CuriousTech/WiFiWaterbedHeater3/Waterbed3/THSensor.cpp

#include "THSensor.h"
#include "Display.h"
#include "eeMem.h"
#include <Wire.h>

extern void WsSend(String s);
extern void sendState(void);

THSensor::THSensor()
{ 
}

void THSensor::init()
{
  Wire.begin(11, 10, 100000); // 10,11 also used by RTC and IMU
}

void THSensor::service()
{
  static uint8_t read_delay = 2;
  static uint8_t errCnt = 0;

  if(--read_delay)
    return;

  int16_t temp;
  int16_t rh;
  if(am.measure(temp, rh))
  {
    if(!ee.bCF)
      temp = temp * 9 / 5 + 320;
    tempMedian.add(temp);
    if (tempMedian.getMedian(temp) == tempMedian.OK)
    {
      m_temp = temp;
      m_rh = rh;
    }
    errCnt = 0;
  }
  else
  {
    if(errCnt < 5)
      errCnt++;
    else
    {
      IPAddress ip;
      display.Notify("AM2320 Error", ip); // be annoying
    }
  }

  read_delay = 5; // update every 5 seconds
}
