CuriousTech/WiFiWaterbedHeater3/Waterbed3/digitalFont.h

//
//

const uint8_t DIGIRT_18pt7bBitmaps[] PROGMEM = {
  0x00, 0x04, 0x30, 0xC3, 0x0C, 0x31, 0xC7, 0x1C, 0x61, 0x84, 0x30, 0xE3,
  0x0C, 0x30, 0xC7, 0x18, 0x60, 0x04, 0x38, 0x40, 0x69, 0xFF, 0xBE, 0x50,
  0x03, 0xFF, 0x01, 0xFF, 0xE0, 0xFF, 0xFC, 0x79, 0xCF, 0x1E, 0x77, 0x87,
  0xDD, 0xE1, 0xF6, 0xF8, 0x7F, 0xFE, 0x1B, 0xFB, 0x8E, 0x7C, 0xE3, 0x9E,
  0x30, 0xFF, 0xFC, 0x1F, 0xFE, 0x0F, 0xFF, 0x83, 0x1C, 0x71, 0xCF, 0x98,
  0x77, 0xEE, 0x1F, 0xFF, 0x87, 0xFB, 0xE1, 0xEE, 0xF8, 0xFB, 0xBE, 0x3C,
  0xE7, 0x0E, 0x39, 0xC1, 0xFF, 0xE0, 0x3F, 0xF0, 0x00, 0x00, 0x20, 0x00,
  0x70, 0x00, 0xF0, 0x07, 0xFE, 0x0F, 0xFF, 0x1F, 0xFC, 0x30, 0xE0, 0x30,
  0xE0, 0x31, 0xC0, 0x39, 0xC0, 0x31, 0xC0, 0x70, 0x80, 0x70, 0x80, 0x70,
  0x80, 0x7F, 0xF8, 0x3F, 0xFC, 0x1F, 0xFC, 0x03, 0x0C, 0x03, 0x1C, 0x03,
  0x1C, 0x07, 0x1C, 0x07, 0x1C, 0x07, 0x1C, 0x07, 0x18, 0x07, 0x18, 0x7F,
  0xF8, 0xFF, 0xF0, 0x7F, 0xE0, 0x0E, 0x00, 0x0E, 0x00, 0x0C, 0x00, 0x03,
  0xFF, 0x01, 0xFF, 0xE0, 0xFF, 0xFC, 0x79, 0xCF, 0x1E, 0x77, 0x87, 0xDD,
  0xE1, 0xF6, 0xF8, 0x7F, 0xFE, 0x1B, 0xFB, 0x8E, 0x7C, 0xE3, 0x9E, 0x30,
  0xFF, 0xFC, 0x1F, 0xFE, 0x0F, 0xFF, 0x83, 0x1C, 0x71, 0xCF, 0x98, 0x77,
  0xEE, 0x1F, 0xFF, 0x87, 0xFB, 0xE1, 0xEE, 0xF8, 0xFB, 0xBE, 0x3C, 0xE7,
  0x0E, 0x39, 0xC1, 0xFF, 0xE0, 0x3F, 0xF0, 0x00, 0x03, 0xFF, 0x03, 0xFF,
  0xC3, 0xFF, 0x83, 0x00, 0x01, 0x80, 0x00, 0xC0, 0x00, 0x70, 0x00, 0x38,
  0x00, 0x3C, 0x00, 0x1C, 0x00, 0x0E, 0x00, 0x07, 0xE0, 0x01, 0xF8, 0x01,
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
  {   259,   7,  10,   8,    1,   -9 },   // 0x46 'F'
  {   268,   9,  10,  11,    1,   -9 },   // 0x47 'G'
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

const GFXfont FreeSans7pt7b PROGMEM = {
  (uint8_t  *)FreeSans7pt7bBitmaps,
  (GFXglyph *)FreeSans7pt7bGlyphs,
  0x20, 0x7E, 23 };

// Approx. 1354 bytes
