CuriousTech/WiFiWaterbedHeater3/Waterbed3/jsonString.h

#include "eeMem.h"
#include "Media.h"

class jsonString
{
public:
  jsonString(const char *pLabel = NULL)
  {
    m_cnt = 0;
    s = String("{");
    if(pLabel)
    {
      s += "\"cmd\":\"";
      s += pLabel, s += "\",";
    }
  }
        
  String Close(void)
  {
    s += "}";
    return s;
  }

  void Var(const char *key, int iVal)
  {
    if(m_cnt) s += ",";
    s += "\"";
    s += key;
    s += "\":";
    s += iVal;
    m_cnt++;
  }

  void Var(const char *key, uint32_t iVal)
  {
    if(m_cnt) s += ",";
    s += "\"";
    s += key;
    s += "\":";
    s += iVal;
    m_cnt++;
  }

  void Var(const char *key, long int iVal)
  {
    if(m_cnt) s += ",";
    s += "\"";
    s += key;
    s += "\":";
    s += iVal;
    m_cnt++;
  }

  void Var(const char *key, float fVal)
  {
    if(m_cnt) s += ",";
    s += "\"";
    s += key;
    s += "\":";
    s += fVal;
    m_cnt++;
  }
  
  void Var(const char *key, bool bVal)
  {
    if(m_cnt) s += ",";
    s += "\"";
    s += key;
    s += "\":";
    s += bVal ? 1:0;
    m_cnt++;
  }
  
  void Var(const char *key, const char *sVal)
  {
    if(m_cnt) s += ",";
    s += "\"";
    s += key;
    s += "\":\"";
    s += sVal;
    s += "\"";
    m_cnt++;
  }
  
  void Var(const char *key, String sVal)
  {
    if(m_cnt) s += ",";
    s += "\"";
    s += key;
    s += "\":\"";
    s += sVal;
    s += "\"";
    m_cnt++;
  }

  void VarNoQ(const char *key, String sVal) // Lazy hack
  {
    if(m_cnt) s += ",";
    s += "\"";
    s += key;
    s += "\":";
    s += sVal;
    m_cnt++;
  }

  void Array(const char *key, String sVal[], int n)
  {
    if(m_cnt) s += ",";
    s += "\"";
    s += key;
    s += "\":[";
    for(int i = 0; i < n; i++)
    {
      if(i) s += ",";
      s += "\"";
      s += sVal[i];
      s += "\"";
    }
    s += "]";
    m_cnt++;
  }

  void Array(const char *key, uint8_t iVal[], int n)
  {
    if(m_cnt) s += ",";
    s += "\"";
    s += key;
    s += "\":[";
    for(int i = 0; i < n; i++)
    {
      if(i) s += ",";
      s += iVal[i];
    }
    s += "]";
    m_cnt++;
  }

  void Array(const char *key, uint16_t iVal[], int n)
  {
    if(m_cnt) s += ",";
    s += "\"";
    s += key;
    s += "\":[";
    for(int i = 0; i < n; i++)
    {
      if(i) s += ",";
      s += iVal[i];
    }
    s += "]";
    m_cnt++;
  }

  void Array(const char *key, uint32_t iVal[], int n)
  {
    if(m_cnt) s += ",";
    s += "\"";
    s += key;
    s += "\":[";
    for(int i = 0; i < n; i++)
    {
      if(i) s += ",";
      s += iVal[i];
    }
    s += "]";
    m_cnt++;
  }

  void Array(const char *key, float fVal[], int n)
  {
    if(m_cnt) s += ",";
    s += "\"";
    s += key;
    s += "\":[";
    for(int i = 0; i < n; i++)
    {
      if(i) s += ",";
      if(fVal[i] == (int)fVal[i]) // reduces size
        s += (int)fVal[i];
      else
        s += fVal[i];
    }
    s += "]";
    m_cnt++;
  }

 // custom arrays for waterbed
  void Array(const char *key, Sched schVal[][MAX_SCHED], int n)
  {
    if(m_cnt) s += ",";
    s += "\"";
    s += key;
    s += "\":[";

    for(int i2 = 0; i2 < n; i2++)
    {
      if(i2) s += ",";
      s += "[";
      for(int i = 0; i < MAX_SCHED; i++)
      {
        if(i) s += ",";
        s += "[";
        s += schVal[i2][i].timeSch;
        s += ","; s += String( (float)schVal[i2][i].setTemp/10, 1 );
        s += ","; s += String( (float)schVal[i2][i].thresh/10,1 );
        s += "]";
      }
      s += "]";
    }
    s += "]";
    m_cnt++;
  }

  void Array(const char *key, FileEntry entry[], bool bAddParent)
  {
    if(m_cnt) s += ",";
    s += "\"";
    s += key;
    s += "\":[";

    if(bAddParent)
      s += "[\"..\",0,1,0],";
    for(int i = 0; entry[i].Name[0]; i++)
    {
      if(i) s += ",";
      s += "[\"";
      s += entry[i].Name;
      s += "\",";
      s += entry[i].Size;
      s += ",";
      s += entry[i].bDir;
      s += ",";
      s += entry[i].Date;
      s += "]";
    }
    s += "]";
    m_cnt++;
  }

  void ArrayCost(const char *key, uint16_t iVal[], int n)
  {
    if(m_cnt) s += ",";
    s += "\"";
    s += key;
    s += "\":[";
    for(int i = 0; i < n; i++)
    {
      if(i) s += ",";
      s += (float)iVal[i]/100;
    }
    s += "]";
    m_cnt++;
  }

  void ArrayPts(const char *key, int16_t pts[][2], int n)
  {
    if(m_cnt) s += ",";
    s += "\"";
    s += key;
    s += "\":[";
    for(int i = 0; i < n; i++)
    {
      if(i) s += ",";
      s += '[';
      s += pts[i][0];
      s += ',';
      s += pts[i][1];
      s += ']';
    }
    s += "]";
    m_cnt++;
  }
protected:
  String s;
  int m_cnt;
};
